Naesstrom/Airrohr-kit/images/box_front.jpg

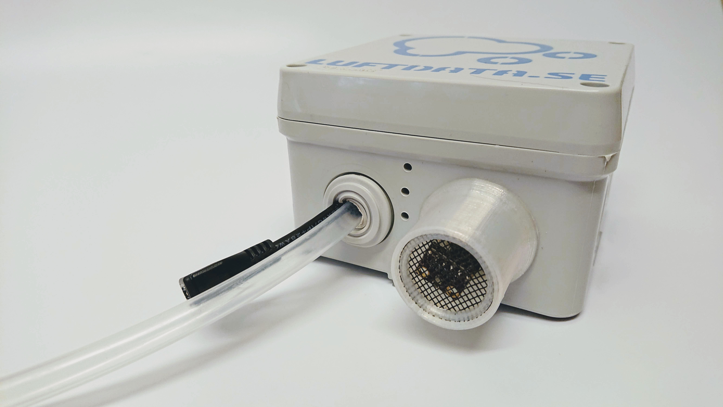
images/box_front.jpg
