Naesstrom/Airrohr-kit/images/box_with_lid.jpg

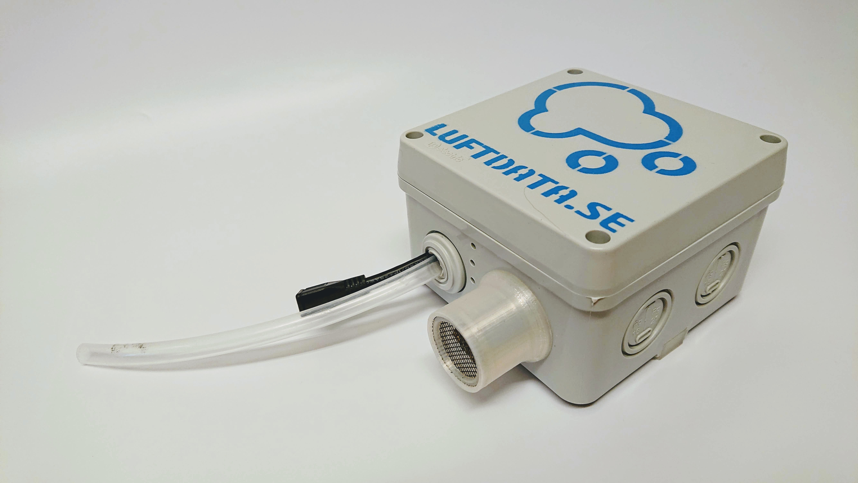
images/box_with_lid.jpg
